bzizou/bmso_all_sky_cam/pictures/resized/PXL_20251206_172132660.jpg

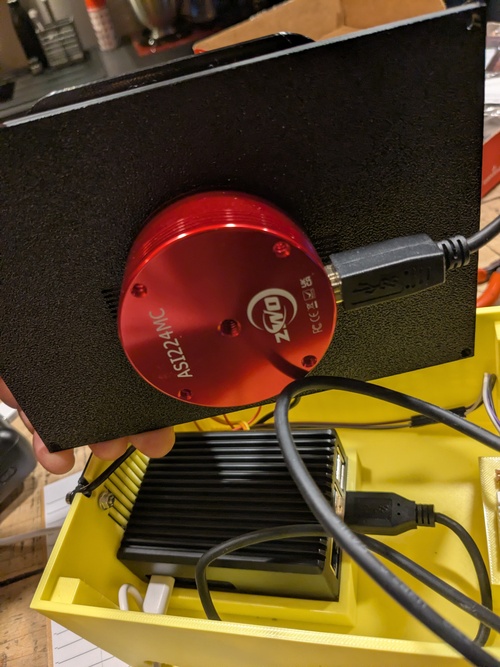
pictures/resized/PXL_20251206_172132660.jpg
