bzizou/bmso_all_sky_cam/pictures/resized/PXL_20251212_172759677.jpg

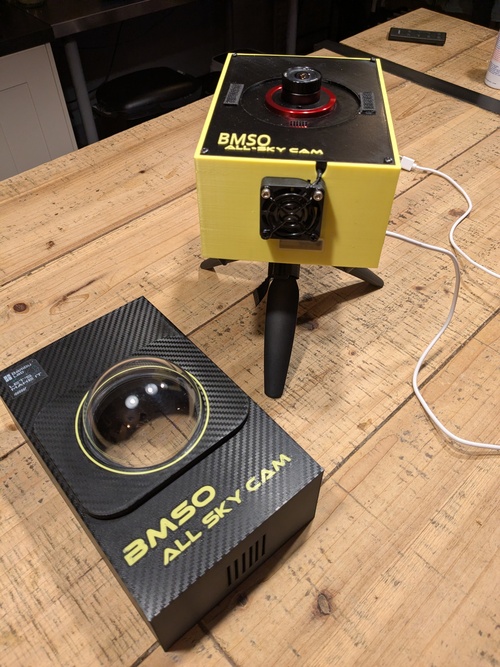
pictures/resized/PXL_20251212_172759677.jpg
