bzizou/bmso_all_sky_cam/pictures/resized/PXL_20251212_172814877.jpg

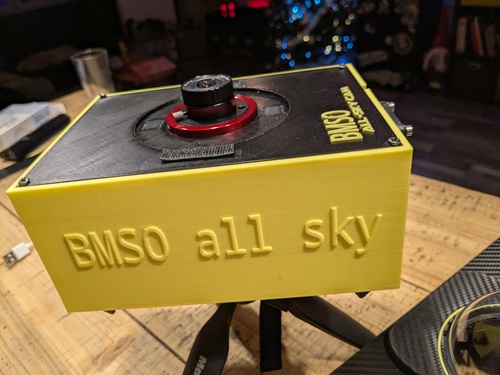
pictures/resized/PXL_20251212_172814877.jpg
