bzizou/bmso_all_sky_cam/pictures/resized/PXL_20260118_141939361.jpg

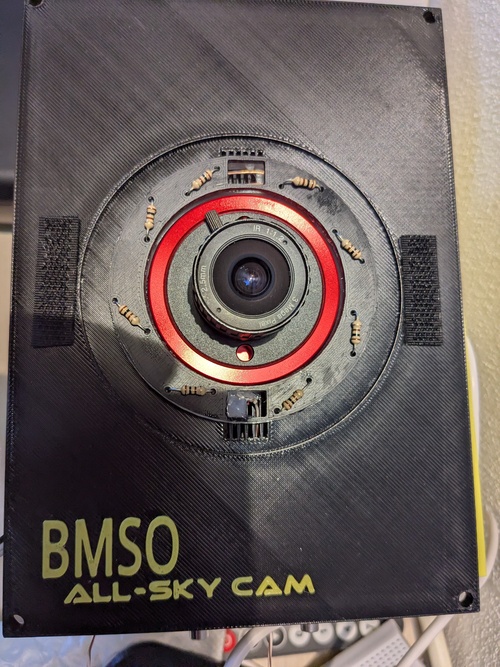
pictures/resized/PXL_20260118_141939361.jpg
