bzizou/bmso_all_sky_cam/pictures/resized/PXL_20260118_142048376.jpg

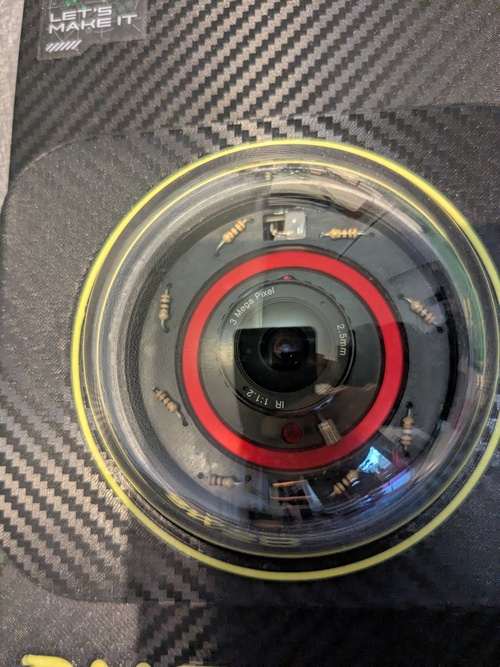
pictures/resized/PXL_20260118_142048376.jpg
