bzizou/bmso_all_sky_cam/pictures/resized/PXL_20260118_172114990.jpg

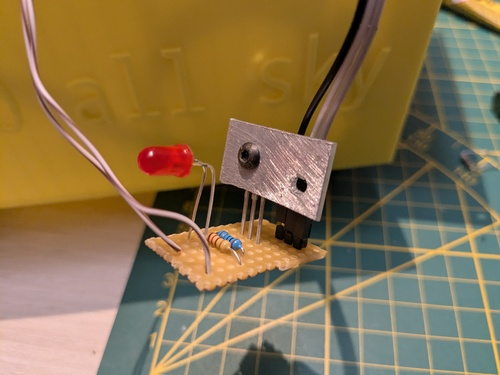
pictures/resized/PXL_20260118_172114990.jpg
