bzizou/bmso_all_sky_cam/pictures/resized/PXL_20260118_172637907.jpg

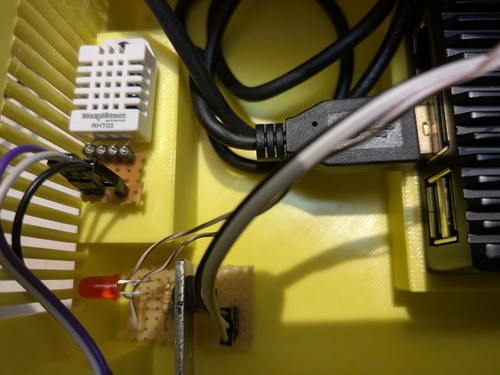
pictures/resized/PXL_20260118_172637907.jpg
