bzizou/bmso_all_sky_cam/pictures/resized/PXL_20260118_173032413.jpg

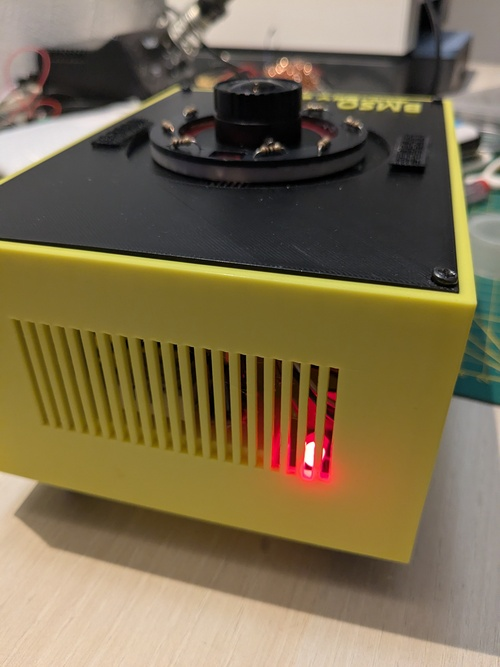
pictures/resized/PXL_20260118_173032413.jpg
