bzizou/bmso_all_sky_cam/pictures/resized/PXL_20260118_174407876.jpg

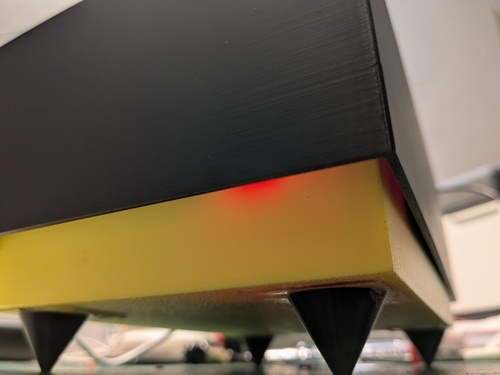
pictures/resized/PXL_20260118_174407876.jpg
