bzizou/bmso_all_sky_cam/pictures/resized/screenshot1.png

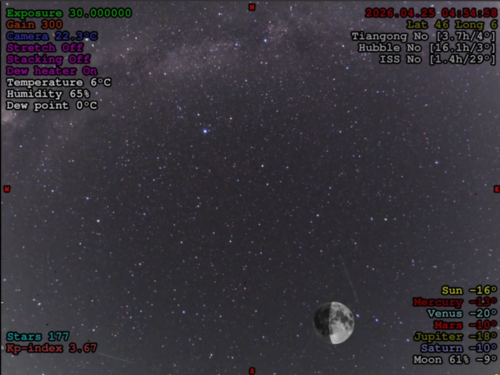
pictures/resized/screenshot1.png
